turgu1/ESP32-Sensing-Device/software/.freezer_adc_lut.h

const float ADC_LUT[4096] = { 0,
33.0000,35.0000,37.0000,39.0000,41.0000,43.0000,45.0000,47.0000,48.8000,50.0000,51.6000,52.8000,54.0000,55.4000,56.8000,
58.0000,59.2000,60.8000,61.8000,63.0000,64.4000,65.2000,66.0000,67.0000,68.0000,69.0000,69.8000,70.8000,71.8000,72.8000,
73.6000,74.4000,75.2000,76.0000,77.0000,78.0000,78.8000,79.8000,80.8000,82.0000,83.2000,84.6000,85.8000,86.8000,88.0000,
89.0000,90.4000,91.8000,92.8000,94.0000,95.0000,96.4000,97.4000,98.6000,99.6000,100.6000,101.8000,102.8000,103.8000,104.8000,
105.8000,106.8000,107.8000,108.8000,109.8000,110.8000,112.0000,113.0000,114.2000,115.6000,116.8000,118.0000,119.0000,120.4000,121.8000,
122.8000,124.0000,125.2000,126.8000,127.8000,128.8000,130.0000,131.0000,132.0000,133.0000,134.0000,135.2000,136.4000,137.4000,138.6000,
139.8000,140.8000,141.8000,142.8000,143.8000,144.8000,145.8000,146.8000,147.8000,148.8000,149.8000,150.8000,151.8000,152.8000,153.6000,
154.6000,155.6000,156.4000,157.4000,158.4000,159.2000,160.2000,161.4000,162.4000,163.6000,164.8000,165.8000,166.8000,167.8000,168.8000,
170.0000,171.0000,172.0000,173.0000,174.0000,175.2000,176.2000,177.4000,178.8000,179.8000,180.8000,182.0000,183.0000,184.0000,185.2000,
186.4000,187.6000,188.8000,189.8000,190.8000,192.0000,193.0000,194.4000,195.8000,197.0000,198.0000,199.4000,200.8000,201.8000,203.0000,
204.4000,205.8000,206.8000,208.0000,209.0000,210.0000,210.8000,211.8000,212.8000,213.4000,214.2000,215.0000,216.0000,217.0000,217.8000,
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
650.8000,652.0000,653.0000,654.0000,655.0000,656.0000,657.0000,658.0000,659.0000,660.2000,661.2000,662.4000,663.6000,664.8000,665.8000,
666.8000,667.8000,668.8000,670.0000,671.0000,672.0000,673.0000,674.0000,675.0000,676.0000,677.2000,678.2000,679.2000,680.4000,681.4000,
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
};
